senadurarslan/Raspberry-Pi-Image-Processing-HAT/mühtas_1_project/ov2640_regs.c

// ov2640_regs.c
#include "ov2640_regs.h"

// Kullanılan sentinel değerleri:
#define REG_TERM_8BIT 0xFF
#define VAL_TERM_8BIT 0xFF

// =============================
// OV2640 INIT REGISTER TABLE
// (ArduCAM'ın orijinal init dizisi)
// =============================

const struct sensor_reg ov2640_init_reg_tbl[] = {
    {0xff, 0x01},
    {0x12, 0x80}, // reset
    {0xff, 0x00},
    {0x2c, 0xff},
    {0x2e, 0xdf},
    {0xff, 0x01},
    {0x3c, 0x32},
    {0x11, 0x00},
    {0x09, 0x02},
    {0x04, 0x28},
    {0x13, 0xe5},
    {0x14, 0x48},
    {0x2c, 0x0c},
    {0x33, 0x78},
    {0x3a, 0x33},
    {0x3b, 0xfb},
    {0x3e, 0x00},
    {0x43, 0x11},
    {0x16, 0x10},
    {0x39, 0x02},
    {0x35, 0x88},
    {0x22, 0x0a},
    {0x37, 0x40},
    {0x23, 0x00},
    {0x34, 0xa0},
    {0x06, 0x02},
    {0x06, 0x88},
    {0x07, 0xc0},
    {0x0d, 0xB7},
    {0x0e, 0x01},
    {0x4c, 0x00},
    {0x4a, 0x81},
    {0x21, 0x99},
    {0x24, 0x40},
    {0x25, 0x38},
    {0x26, 0x82},
    {0x5c, 0x00},
    {0x63, 0x00},
    {0x46, 0x22},
    {0x0c, 0x3c},
    {0x61, 0x70},
    {0x62, 0x80},
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
    {REG_TERM_8BIT, VAL_TERM_8BIT}
};


// ============================================
// OV2640 QQVGA JPEG (160x120) REGISTER TABLE
// ============================================

const struct sensor_reg ov2640_qqvga_jpeg_tbl[] = {
    {0xff, 0x01},
    {0x12, 0x40}, // JPEG mode
    {0x17, 0x11},
    {0x18, 0x75},
    {0x19, 0x01},
    {0x1a, 0x97},
    {0x32, 0x36},
    {0x4f, 0xbb},
    {0x50, 0x9c},
    {0x5a, 0x57},
    {0x6d, 0x80},
    {0x39, 0x02},
    {0x35, 0x88},
    {0x22, 0x0a},
    {0x37, 0x40},
    {0x23, 0x00},
    {0x34, 0xa0},
    {0x06, 0x02},
    {0x06, 0x88},
    {0xff, 0x00},
    {0xc0, 0x64},
    {0xc1, 0x4b},
    {0x86, 0x35},
    {0x50, 0x89},
    {0x51, 0xc8},
    {0x52, 0x96},
    {0x53, 0x00},
    {0x54, 0x00},
    {0x55, 0x00},
    {0x57, 0x00},
    {0x5a, 0x2c}, // width 160
    {0x5b, 0x1e}, // height 120
    {0x5c, 0x00},
    {0xd3, 0x82},
    {REG_TERM_8BIT, VAL_TERM_8BIT}
};
